whatwareweb/usb-dac/assembly/board1/2024-08-06-16-54-55-373.jpg

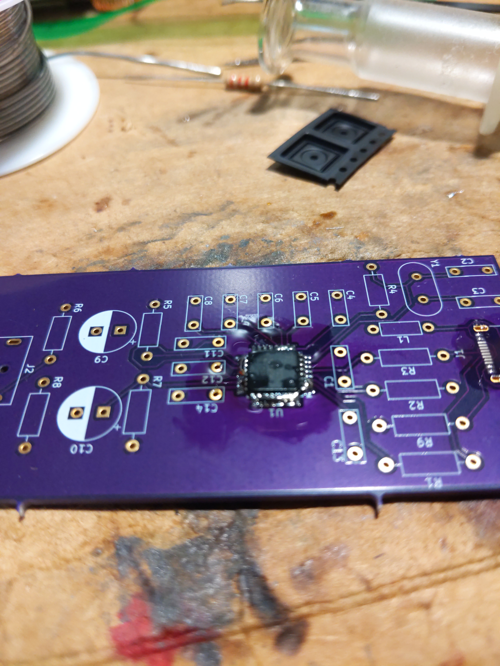
assembly/board1/2024-08-06-16-54-55-373.jpg
