whatwareweb/usb-dac/assembly/board1/2024-08-06-17-01-31-405.jpg

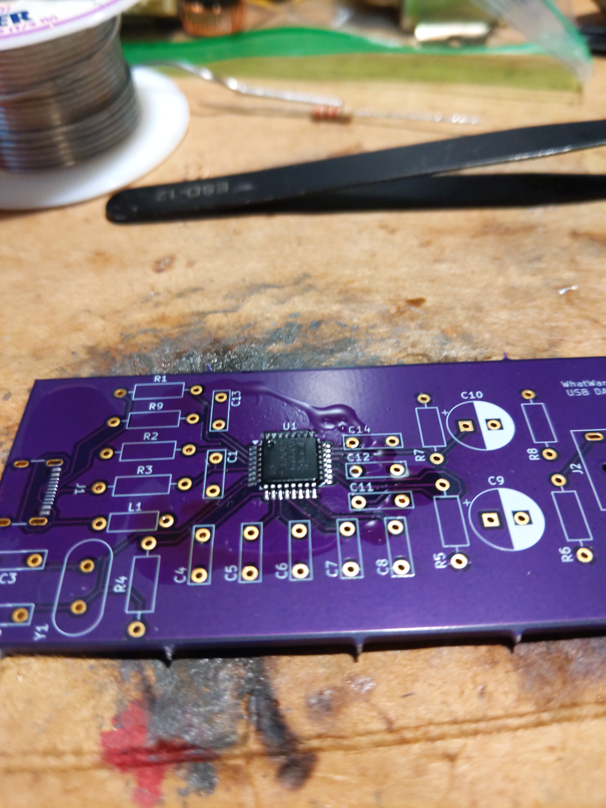
assembly/board1/2024-08-06-17-01-31-405.jpg
