whatwareweb/usb-dac/assembly/board1/2024-08-06-17-08-24-996.jpg

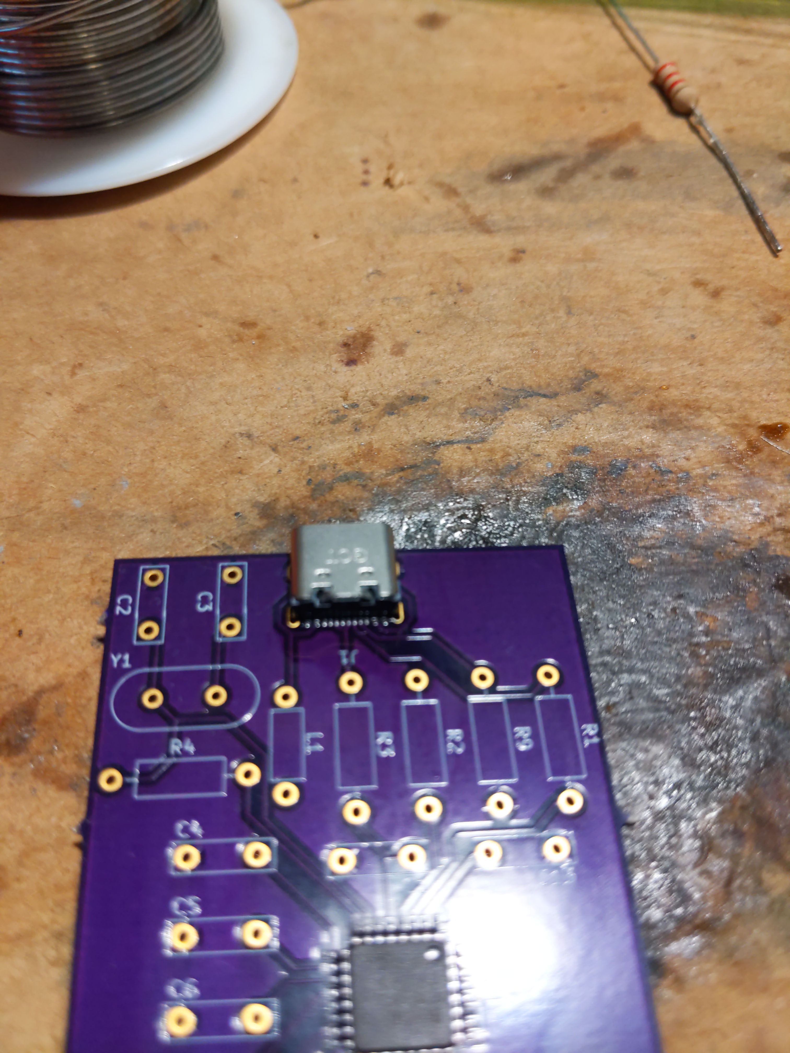
assembly/board1/2024-08-06-17-08-24-996.jpg
