whatwareweb/usb-dac/assembly/board1/2024-08-06-17-12-53-256.jpg

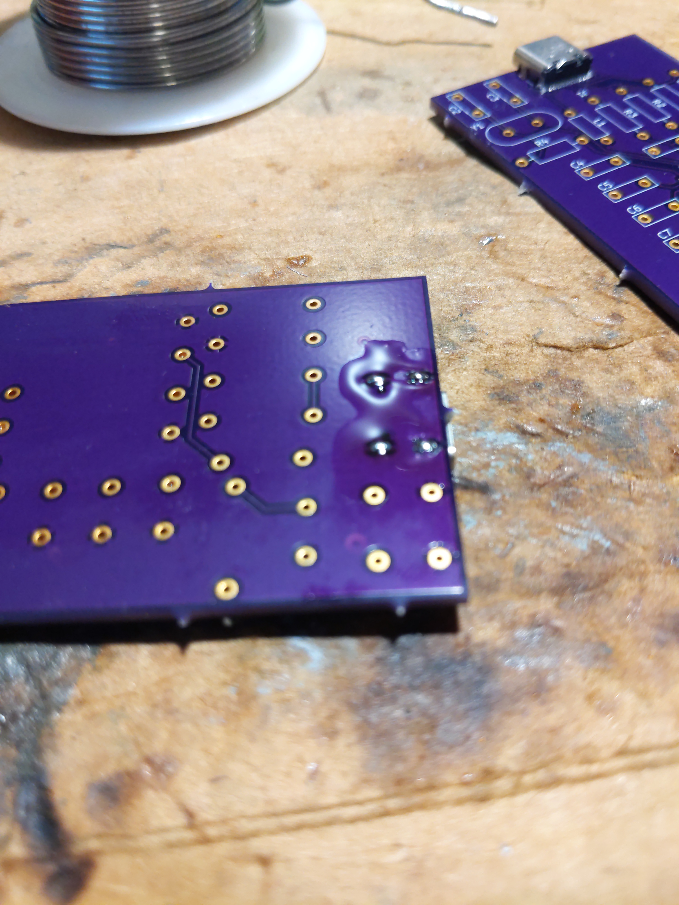
assembly/board1/2024-08-06-17-12-53-256.jpg
