whatwareweb/usb-dac/assembly/board1/2024-08-06-17-56-26-789.jpg

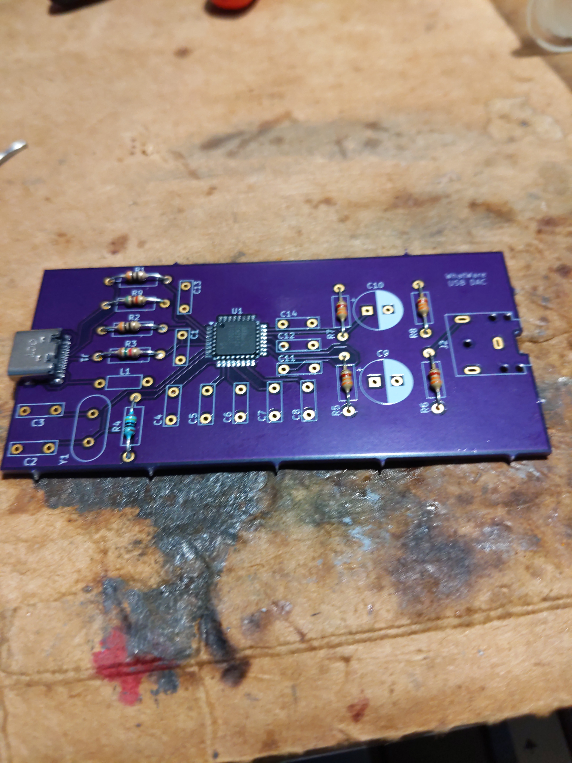
assembly/board1/2024-08-06-17-56-26-789.jpg
