whatwareweb/usb-dac/assembly/board1/2024-08-06-17-58-25-972.jpg

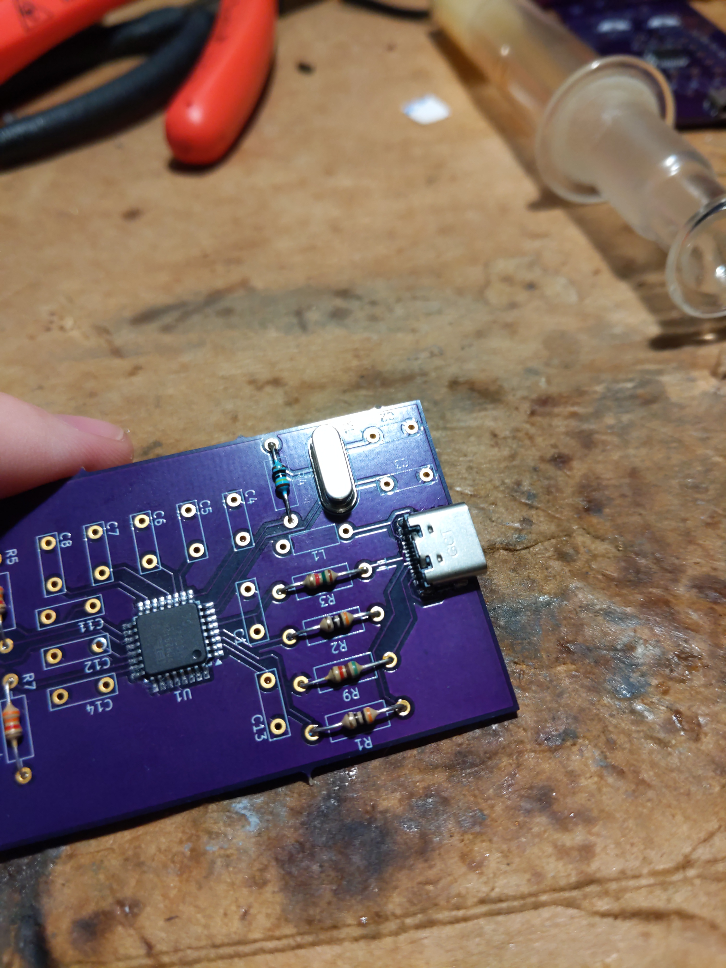
assembly/board1/2024-08-06-17-58-25-972.jpg
