whatwareweb/usb-dac/assembly/board1/2024-08-06-18-04-33-190.jpg

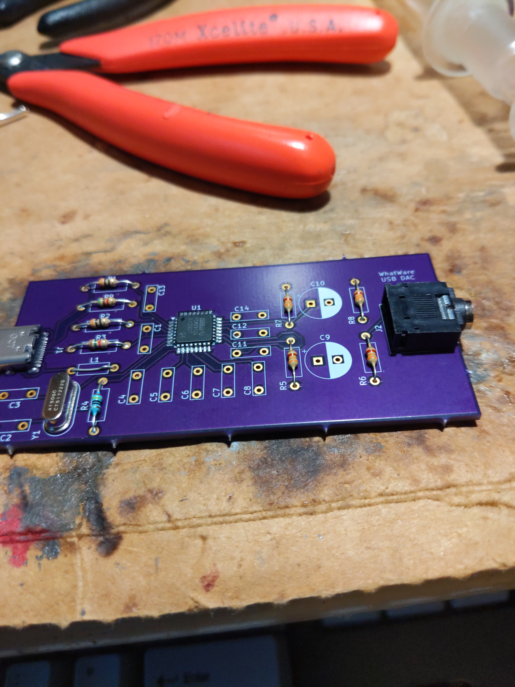
assembly/board1/2024-08-06-18-04-33-190.jpg
