whatwareweb/usb-dac/assembly/board2/2024-08-06-20-13-06-226.jpg

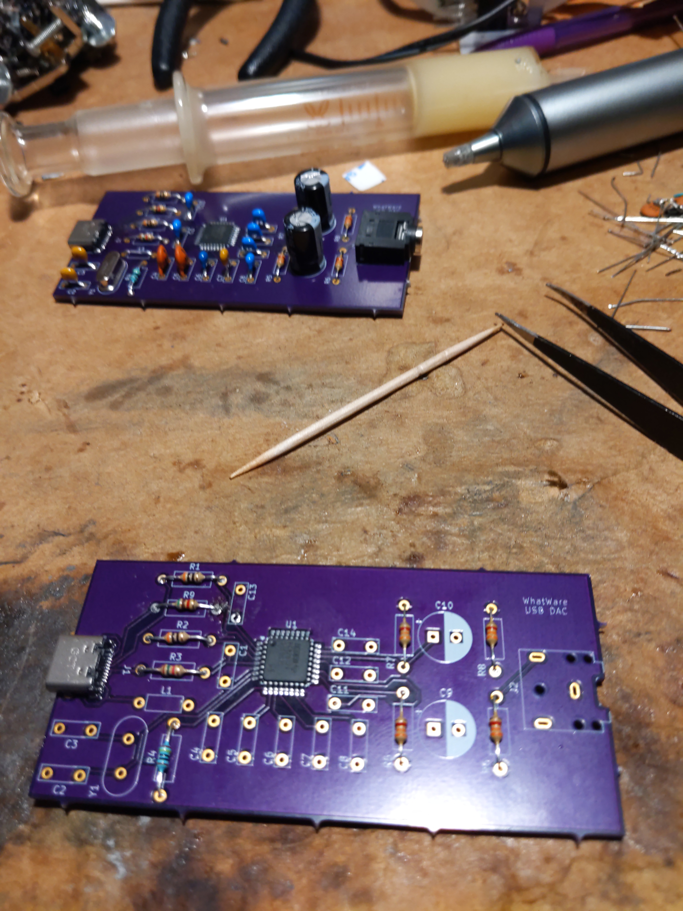
assembly/board2/2024-08-06-20-13-06-226.jpg
